Kiran1510/Motor-Control/Hardware/Self Balancing Cube.kicad_sch

## KiCad design Hardware/Self Balancing Cube.kicad_sch (2025-12-19)

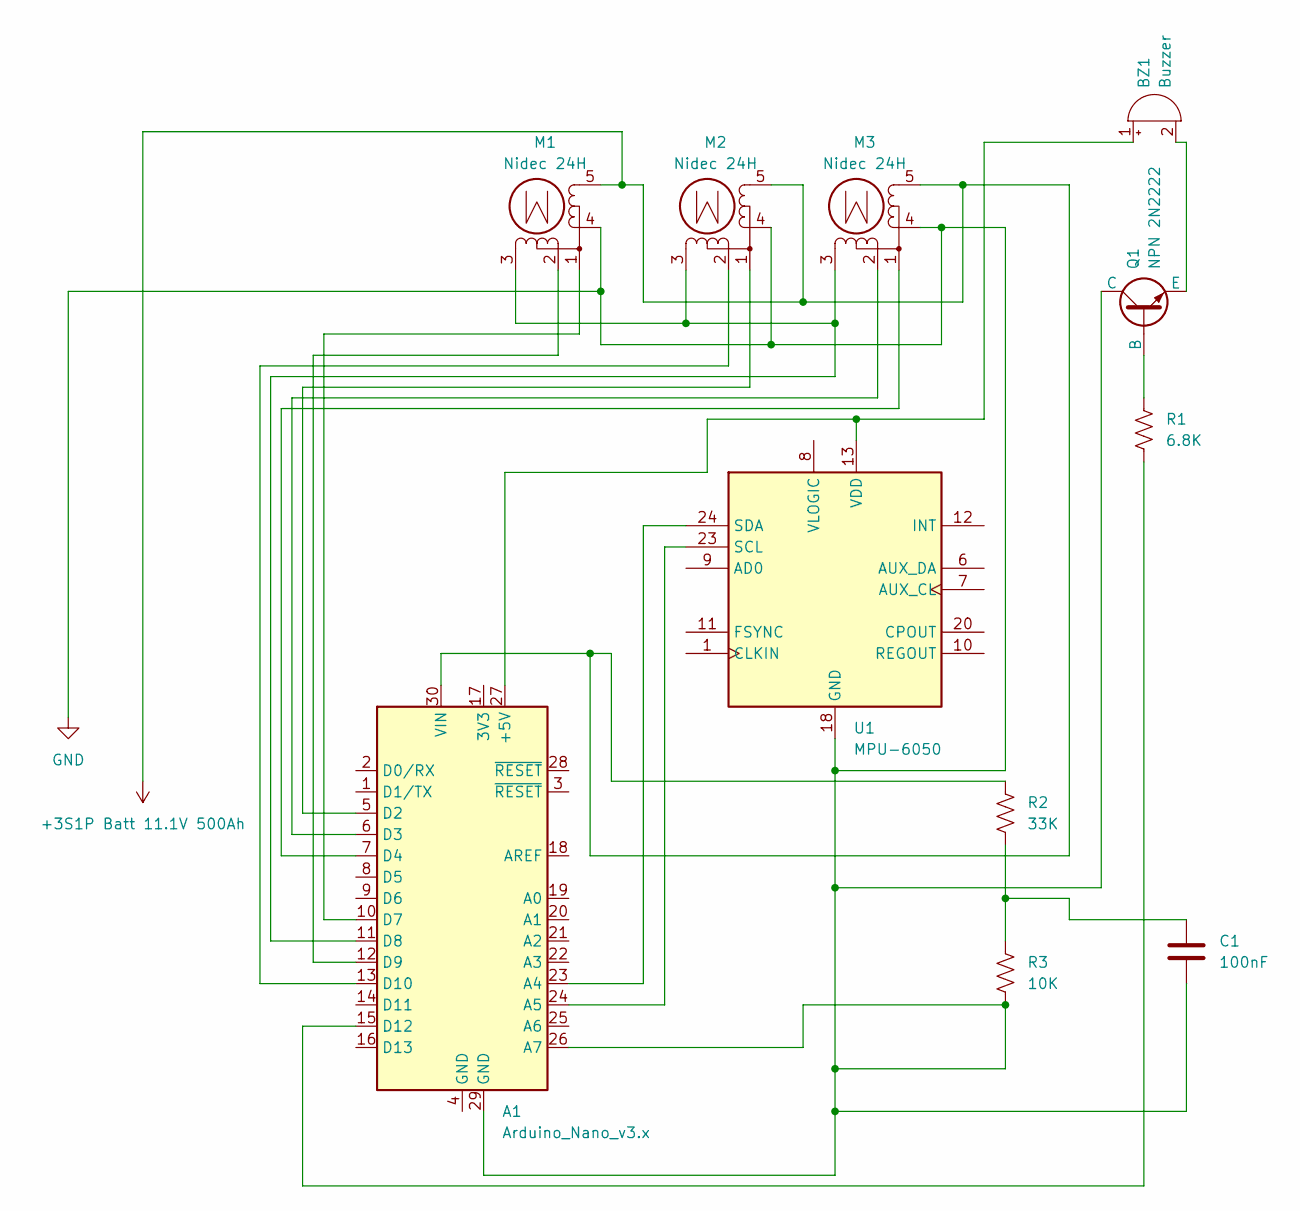
[picture p6: schematic Self Balancing Cube.kicad_sch]

Parts:
A1: Arduino_Nano_v3.x; Arduino_Nano
BZ1: Buzzer
C1: 100nF
M1, M2, M3: Nidec 24H
Q1: NPN 2N2222; TO-39-3
R1: 6.8K; R_0805_2012Metric
R2: 33K; R_0805_2012Metric
R3: 10K; R_0805_2012Metric
U1: MPU-6050; InvenSense_QFN-24_4x4mm_P0.5mm

Connections:
+3S1P Batt 11.1V 500Ah: A1.30 (VIN), M1.5, M2.5, M3.5, R2.1
GND: A1.26 (A7), A1.29 (GND), C1.2, M1.4, M2.4, M3.4, Q1.1 (C), R3.2, U1.18 (GND)
unnamed: A1.5 (D2), M2.1
unnamed: A1.6 (D3), M3.2
unnamed: A1.7 (D4), M3.1
unnamed: A1.10 (D7), M1.1
unnamed: A1.11 (D8), M1.3 (-), M2.3 (-), M3.3 (-)
unnamed: A1.12 (D9), M1.2
unnamed: A1.13 (D10), M2.2
unnamed: A1.15 (D12), R1.2
unnamed: A1.23 (A4), U1.24 (SDA)
unnamed: A1.24 (A5), U1.23 (SCL)
unnamed: A1.27 (+5V), BZ1.1 (+), U1.13 (VDD)
unnamed: BZ1.2 (-), Q1.3 (E)
unnamed: C1.1, R2.2, R3.1
unnamed: Q1.2 (B), R1.1
